Ilexshadow/Cyber-Wand/外壳/3DShell_实物图.jpg

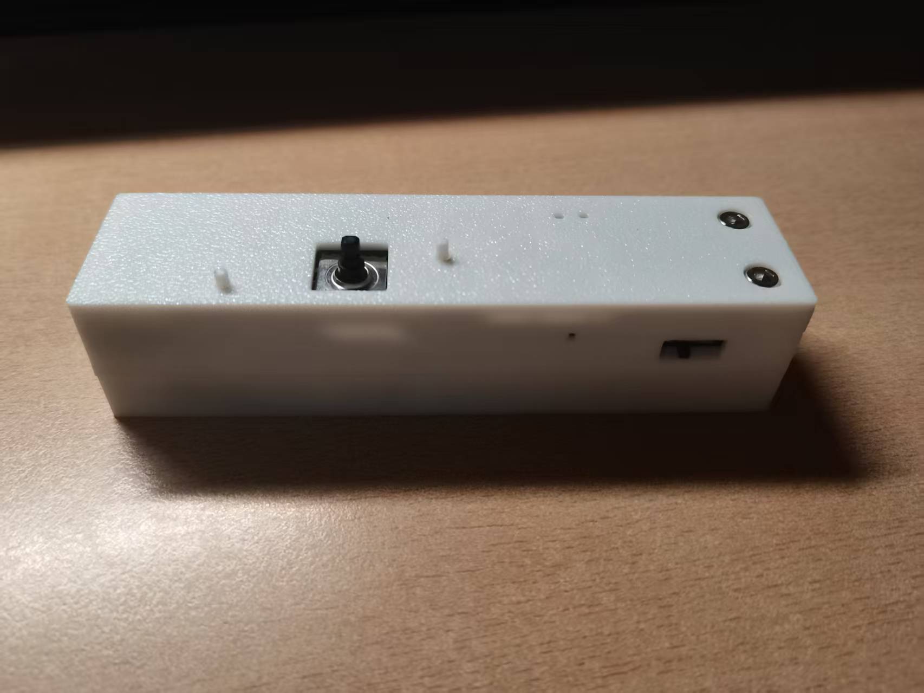
外壳/3DShell_实物图.jpg
