Ilexshadow/Cyber-Wand/代码/C程序-发送-PCB/nnom/weights.h

#include "nnom.h"

/* Weights, bias and Q format */
#define TENSOR_CONV1D_KERNEL_0 {24, 74, 75, -38, 81, 41, -17, 33, -9, 38, -53, -88, -45, -43, -19, 26, -67, -12, -23, 24, 47, -24, 77, 69, -91, 19, 64, -34, -36, -29, -68, -21, 91, -102, -52, 71, -4, -78, -80, 20, -27, 8, 53, -16, -89, 46, -78, -74, 29, -91, -8, 66, -28, -76, 71, 88, -6, 79, 59, -72, 84, 17, -30, -14, 63, 70, 10, 20, 75, 26, 49, 95, 33, 76, -37, 68, 94, 9, -46, 72, -27, -81, 10, -36, -57, 58, -7, 25, -54, -65, -55, 90, 58, -35, 82, 52, -97, 55, 67, -45, 40, 36, 65, -48, 109, 7, -67, 71, 38, 94, 43, 60, 52, 95, 53, 4, 32, 4, -19, 24, -31, -104, -86, 80, -82, -50, 56, -8, 74, -4, 45, 63, 80, -55, 1, -92, 30, 80, -54, -71, 81, -10, 9, 98, 7, -47, -97, -27, -9, -29, -87, 54, -83, -72, 21, 86, -43, 37, 102, 31, -45, 54, -25, -49, 85, -55, -89, 89, -100, -30, 37, -17, 14, -57, 55, -70, -68, -27, -44, -10, -30, -23, 25, -93, -59, -19, -59, -58, 45, 90, -30, 48, 32, 11, -7, 24, -73, -4, -96, -79, 21, -84, -76, -10, -105, 26, -7, -28, -100, -86, 37, -12, -50, 74, -80, -71, -102, -28, 77, -88, -70, 1, -66, -45, 35, -71, -40, -5, -90, -55, -20, -29, -18, 8, 37, 100, 99, -8, 51, 29, -4, 72, -12, 88, 83, -37, 57, -8, 66, 1, 36, 38, 28, -71, 42, -6, 35, 91, -49, -50, 50, 36, 73, -70, 85, 68, 33, 35, 34, -60}

#define TENSOR_CONV1D_KERNEL_0_DEC_BITS {8}

#define TENSOR_CONV1D_BIAS_0 {53, -39, 70, 80, -25, 23, 57, 27, 62, 25, 84, 23, 90, -16, 74, 57, 85, 75, 75, -38, 33, 36, 43, 10, 25, 35, 87, 102, 13, 92}

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

#define TENSOR_CONV1D_1_KERNEL_0_DEC_BITS {8}

#define TENSOR_CONV1D_1_BIAS_0 {98, 0, 14, 12, 70, 1, 92, -38, -54, 19, 69, 53, -55, 108, -18}

#define TENSOR_CONV1D_1_BIAS_0_DEC_BITS {10}

#define CONV1D_1_BIAS_LSHIFT {2}

#define CONV1D_1_OUTPUT_RSHIFT {9}

#define TENSOR_DENSE_KERNEL_0 {34, 87, -73, 34, 6, -62, 37, -13, -118, 4, 98, 1, 45, 20, 36, -55, -52, -46, 45, 43, -49, 27, 8, -63, 10, -16, 31, 30, -91, 23, -55, -7, 11, 7, -45, 41, -36, 42, -44, 14, -32, 23, -126, -17, 67, -1, -14, -33, -31, -14, -61, -57, -4, 53, 30, -97, -75, 19, 48, 28, -23, 44, 83, 9, -6, 92, 7, -50, 3, -35, 40, -26, 95, 90, -21, 56, 4, 32, -27, -24, 65, -112, 59, -65, 88, -54, 77, -80, -18, -22, 24, -82, -108, 50, 73, 18, -112, 78, 82, 16, 37, 36, -36, 30, -24, 93, 42, 52, -67, -9, 90, 36, 55, 87, -19, 64, -71, -31, 22, -65, 30, -32, 64, -86, -35, 7, -109, 104, -14, 27, -22, -34, 33, 109, -114, 24, -114, -54, -11, -109, 34, -17, -62, -103, 55, 14, 3, 22, -22, -81, 65, 3, -78, -41, 74, -38, -21, 83, 47, 52, 80, 9, -17, 17, 0, -86, -96, 66, -94, -33, -27, -40, 82, -14, -5, 84, 100, -87, 82, 51, 45, 8, -32, 41, 17, -3, 10, 79, -51, -54, -68, -14, -75, -56, -43, -34, -114, 19, 14, -99, 32, 52, 63, -91, 38, -111, 16, -21, -4, 13, -28, -32, -58, 0, -79, 60, -44, -90, 2, -18, -65, 84, -89, 11, -60, -112, 91, 45, -102, 1, -100, -33, 28, -90, 57, -109, 43, -61, 33, -49, -44, 54, 48, -10, 19, 7, 74, -17, -49, 2, 8, 1, 91, 24, 79, -53, 80, -58, -77, 0, 8, -17, 90, -76, -35, -58, 54, -49, -122, -52, -3, 63, -17, 60, -78, -28, -4, -56, -29, -91, -113, 73, -52, 27, -46, -20, 15, -10, 95, -106, 75, -88, -102, 25, -111, 35, -28, 52, -76, 38, 17, 5, 73, 6, -30, -8, 21, 26, 19, -57, -73, 67, 16, -35, 16, 33, -88, -23, 49, -67, -56, 7, 94, 91, 61, 6, -103, -1, -37, 11, -1, -40, -88, 47, -57, 10, 5, -68, 50, -48, 69, 58, -101, 22, 61, 44, 43, -3, 28, 20, -62, 18, -28, -75, -11, -41, -71, -95, 15, 49, -47, 72, -73, -24, 84, -19, 47, -16, -7, -54, 38, -89, 52, -66, -3, 66, 53, -20, -7, -25, -88, -66, 33, 59, -53, -17, -69, 45, 85, 73, 47, -52, 34, -46, 20, 21, -66, 20, -94, -77, -16, -21, -42, 16, 9, 49, 8, -28, -3, -6, 106, 32, 16, 92, 51, 9, 36, -60, 80, 66, 28, 85, -23, -71, -5, 13, 72, -45, 86, -32, 50, -3, -34, 73, 10, -11, 22, -78, 9, -4, -8, -73, 79, 26, -32, -64, 87, 53, 4, 85, -71, 72, 12, 51, 30, 24, -3, 29, 47, 1, -35, 67, 63, 59, 87, 43, 117, -59, -7, 52, 70, -87, -100, 77, -70, -124, -27, 16, 8, -7, 84, -46, 57, -90, 41, 75, -72, -39, -67, -46, -45, -84, 20, -68, 96, -12, -39, -37, 52, 30, -47, 40, -41, 67, -28, 61, 78, 37, 64, -93, 87, -80, -3, 37, -98, -64, -60, 37, -23, -74, -2, 4, -42, -42, -85, -87, -28, -75, -35, 8, 74, -118, -24, -5, 104, -9, -73, 50, -34, -88, -38, 8, 16, 11, 1, 43, 9, -6, 38, 6, 34, 61, -6, 23, -11, -109, -57, 26, 34, -37, -13, -46, -98, -73, -72, 81, 23, -6, -67, 55, -65, -38, 52, 61, -20, -10, 64, 49, 71, -103, 42, 82, 59, -36, -23, -44, 16, 84, -41, 60, 45, -62, -22, 82, -116, 100, -37, 37, -24, 17}

#define TENSOR_DENSE_KERNEL_0_DEC_BITS {8}

#define TENSOR_DENSE_BIAS_0 {-44, 81, -31, -89, -63, -3, 64, 24, 40, 24}

#define TENSOR_DENSE_BIAS_0_DEC_BITS {10}

#define DENSE_BIAS_LSHIFT {1}

#define DENSE_OUTPUT_RSHIFT {9}


/* output q format for each layer */
#define INPUT_1_OUTPUT_DEC 5
#define INPUT_1_OUTPUT_OFFSET 0
#define CONV1D_OUTPUT_DEC 4
#define CONV1D_OUTPUT_OFFSET 0
#define LEAKY_RE_LU_OUTPUT_DEC 4
#define LEAKY_RE_LU_OUTPUT_OFFSET 0
#define CONV1D_1_OUTPUT_DEC 3
#define CONV1D_1_OUTPUT_OFFSET 0
#define LEAKY_RE_LU_1_OUTPUT_DEC 3
#define LEAKY_RE_LU_1_OUTPUT_OFFSET 0
#define MAX_POOLING1D_OUTPUT_DEC 3
#define MAX_POOLING1D_OUTPUT_OFFSET 0
#define FLATTEN_OUTPUT_DEC 3
#define FLATTEN_OUTPUT_OFFSET 0
#define DENSE_OUTPUT_DEC 2
#define DENSE_OUTPUT_OFFSET 0
#define SOFTMAX_OUTPUT_DEC 7
#define SOFTMAX_OUTPUT_OFFSET 0

/* bias shift and output shift for none-weighted layer */

/* tensors and configurations for each layer */
static int8_t nnom_input_data[300] = {0};

const nnom_shape_data_t tensor_input_1_dim[] = {100, 3};
const nnom_qformat_param_t tensor_input_1_dec[] = {5};
const nnom_qformat_param_t tensor_input_1_offset[] = {0};
const nnom_tensor_t tensor_input_1 = {
    .p_data = (void*)nnom_input_data,
    .dim = (nnom_shape_data_t*)tensor_input_1_dim,
    .q_dec = (nnom_qformat_param_t*)tensor_input_1_dec,
    .q_offset = (nnom_qformat_param_t*)tensor_input_1_offset,
    .qtype = NNOM_QTYPE_PER_TENSOR,
    .num_dim = 2,
    .bitwidth = 8
};

const nnom_io_config_t input_1_config = {
    .super = {.name = "input_1"},
    .tensor = (nnom_tensor_t*)&tensor_input_1
};
const int8_t tensor_conv1d_kernel_0_data[] = TENSOR_CONV1D_KERNEL_0;

const nnom_shape_data_t tensor_conv1d_kernel_0_dim[] = {3, 3, 30};
const nnom_qformat_param_t tensor_conv1d_kernel_0_dec[] = TENSOR_CONV1D_KERNEL_0_DEC_BITS;
const nnom_qformat_param_t tensor_conv1d_kernel_0_offset[] = {0};
const nnom_tensor_t tensor_conv1d_kernel_0 = {
    .p_data = (void*)tensor_conv1d_kernel_0_data,
    .dim = (nnom_shape_data_t*)tensor_conv1d_kernel_0_dim,
    .q_dec = (nnom_qformat_param_t*)tensor_conv1d_kernel_0_dec,
    .q_offset = (nnom_qformat_param_t*)tensor_conv1d_kernel_0_offset,
    .qtype = NNOM_QTYPE_PER_TENSOR,
    .num_dim = 3,
    .bitwidth = 8
};
const int8_t tensor_conv1d_bias_0_data[] = TENSOR_CONV1D_BIAS_0;

const nnom_shape_data_t tensor_conv1d_bias_0_dim[] = {30};
const nnom_qformat_param_t tensor_conv1d_bias_0_dec[] = TENSOR_CONV1D_BIAS_0_DEC_BITS;
const nnom_qformat_param_t tensor_conv1d_bias_0_offset[] = {0};
const nnom_tensor_t tensor_conv1d_bias_0 = {
    .p_data = (void*)tensor_conv1d_bias_0_data,
    .dim = (nnom_shape_data_t*)tensor_conv1d_bias_0_dim,
    .q_dec = (nnom_qformat_param_t*)tensor_conv1d_bias_0_dec,
    .q_offset = (nnom_qformat_param_t*)tensor_conv1d_bias_0_offset,
    .qtype = NNOM_QTYPE_PER_TENSOR,
    .num_dim = 1,
    .bitwidth = 8
};

const nnom_qformat_param_t conv1d_output_shift[] = CONV1D_OUTPUT_RSHIFT;
const nnom_qformat_param_t conv1d_bias_shift[] = CONV1D_BIAS_LSHIFT;
const nnom_conv2d_config_t conv1d_config = {
    .super = {.name = "conv1d"},
    .qtype = NNOM_QTYPE_PER_TENSOR,
    .weight = (nnom_tensor_t*)&tensor_conv1d_kernel_0,
    .bias = (nnom_tensor_t*)&tensor_conv1d_bias_0,
    .output_shift = (nnom_qformat_param_t *)&conv1d_output_shift, 
    .bias_shift = (nnom_qformat_param_t *)&conv1d_bias_shift, 
    .filter_size = 30,
    .kernel_size = {3},
    .stride_size = {3},
    .padding_size = {0, 0},
    .dilation_size = {1},
    .padding_type = PADDING_SAME
};
const int8_t tensor_conv1d_1_kernel_0_data[] = TENSOR_CONV1D_1_KERNEL_0;

const nnom_shape_data_t tensor_conv1d_1_kernel_0_dim[] = {3, 30, 15};
const nnom_qformat_param_t tensor_conv1d_1_kernel_0_dec[] = TENSOR_CONV1D_1_KERNEL_0_DEC_BITS;
const nnom_qformat_param_t tensor_conv1d_1_kernel_0_offset[] = {0};
const nnom_tensor_t tensor_conv1d_1_kernel_0 = {
    .p_data = (void*)tensor_conv1d_1_kernel_0_data,
    .dim = (nnom_shape_data_t*)tensor_conv1d_1_kernel_0_dim,
    .q_dec = (nnom_qformat_param_t*)tensor_conv1d_1_kernel_0_dec,
    .q_offset = (nnom_qformat_param_t*)tensor_conv1d_1_kernel_0_offset,
    .qtype = NNOM_QTYPE_PER_TENSOR,
    .num_dim = 3,
    .bitwidth = 8
};
const int8_t tensor_conv1d_1_bias_0_data[] = TENSOR_CONV1D_1_BIAS_0;

const nnom_shape_data_t tensor_conv1d_1_bias_0_dim[] = {15};
const nnom_qformat_param_t tensor_conv1d_1_bias_0_dec[] = TENSOR_CONV1D_1_BIAS_0_DEC_BITS;
const nnom_qformat_param_t tensor_conv1d_1_bias_0_offset[] = {0};
const nnom_tensor_t tensor_conv1d_1_bias_0 = {
    .p_data = (void*)tensor_conv1d_1_bias_0_data,
    .dim = (nnom_shape_data_t*)tensor_conv1d_1_bias_0_dim,
    .q_dec = (nnom_qformat_param_t*)tensor_conv1d_1_bias_0_dec,
    .q_offset = (nnom_qformat_param_t*)tensor_conv1d_1_bias_0_offset,
    .qtype = NNOM_QTYPE_PER_TENSOR,
    .num_dim = 1,
    .bitwidth = 8
};

const nnom_qformat_param_t conv1d_1_output_shift[] = CONV1D_1_OUTPUT_RSHIFT;
const nnom_qformat_param_t conv1d_1_bias_shift[] = CONV1D_1_BIAS_LSHIFT;
const nnom_conv2d_config_t conv1d_1_config = {
    .super = {.name = "conv1d_1"},
    .qtype = NNOM_QTYPE_PER_TENSOR,
    .weight = (nnom_tensor_t*)&tensor_conv1d_1_kernel_0,
    .bias = (nnom_tensor_t*)&tensor_conv1d_1_bias_0,
    .output_shift = (nnom_qformat_param_t *)&conv1d_1_output_shift, 
    .bias_shift = (nnom_qformat_param_t *)&conv1d_1_bias_shift, 
    .filter_size = 15,
    .kernel_size = {3},
    .stride_size = {3},
    .padding_size = {0, 0},
    .dilation_size = {1},
    .padding_type = PADDING_SAME
};

const nnom_pool_config_t max_pooling1d_config = {
    .super = {.name = "max_pooling1d"},
    .padding_type = PADDING_VALID,
    .output_shift = 0,
    .kernel_size = {3},
    .stride_size = {3},
    .num_dim = 1
};

const nnom_flatten_config_t flatten_config = {
    .super = {.name = "flatten"}
};
const int8_t tensor_dense_kernel_0_data[] = TENSOR_DENSE_KERNEL_0;

const nnom_shape_data_t tensor_dense_kernel_0_dim[] = {60, 10};
const nnom_qformat_param_t tensor_dense_kernel_0_dec[] = TENSOR_DENSE_KERNEL_0_DEC_BITS;
const nnom_qformat_param_t tensor_dense_kernel_0_offset[] = {0};
const nnom_tensor_t tensor_dense_kernel_0 = {
    .p_data = (void*)tensor_dense_kernel_0_data,
    .dim = (nnom_shape_data_t*)tensor_dense_kernel_0_dim,
    .q_dec = (nnom_qformat_param_t*)tensor_dense_kernel_0_dec,
    .q_offset = (nnom_qformat_param_t*)tensor_dense_kernel_0_offset,
    .qtype = NNOM_QTYPE_PER_TENSOR,
    .num_dim = 2,
    .bitwidth = 8
};
const int8_t tensor_dense_bias_0_data[] = TENSOR_DENSE_BIAS_0;

const nnom_shape_data_t tensor_dense_bias_0_dim[] = {10};
const nnom_qformat_param_t tensor_dense_bias_0_dec[] = TENSOR_DENSE_BIAS_0_DEC_BITS;
const nnom_qformat_param_t tensor_dense_bias_0_offset[] = {0};
const nnom_tensor_t tensor_dense_bias_0 = {
    .p_data = (void*)tensor_dense_bias_0_data,
    .dim = (nnom_shape_data_t*)tensor_dense_bias_0_dim,
    .q_dec = (nnom_qformat_param_t*)tensor_dense_bias_0_dec,
    .q_offset = (nnom_qformat_param_t*)tensor_dense_bias_0_offset,
    .qtype = NNOM_QTYPE_PER_TENSOR,
    .num_dim = 1,
    .bitwidth = 8
};

const nnom_qformat_param_t dense_output_shift[] = DENSE_OUTPUT_RSHIFT;
const nnom_qformat_param_t dense_bias_shift[] = DENSE_BIAS_LSHIFT;
const nnom_dense_config_t dense_config = {
    .super = {.name = "dense"},
    .qtype = NNOM_QTYPE_PER_TENSOR,
    .weight = (nnom_tensor_t*)&tensor_dense_kernel_0,
    .bias = (nnom_tensor_t*)&tensor_dense_bias_0,
    .output_shift = (nnom_qformat_param_t *)&dense_output_shift,
    .bias_shift = (nnom_qformat_param_t *)&dense_bias_shift
};

const nnom_softmax_config_t softmax_config = {
    .super = {.name = "softmax"}
};
static int8_t nnom_output_data[10] = {0};

const nnom_shape_data_t tensor_output0_dim[] = {10};
const nnom_qformat_param_t tensor_output0_dec[] = {SOFTMAX_OUTPUT_DEC};
const nnom_qformat_param_t tensor_output0_offset[] = {0};
const nnom_tensor_t tensor_output0 = {
    .p_data = (void*)nnom_output_data,
    .dim = (nnom_shape_data_t*)tensor_output0_dim,
    .q_dec = (nnom_qformat_param_t*)tensor_output0_dec,
    .q_offset = (nnom_qformat_param_t*)tensor_output0_offset,
    .qtype = NNOM_QTYPE_PER_TENSOR,
    .num_dim = 1,
    .bitwidth = 8
};

const nnom_io_config_t output0_config = {
    .super = {.name = "output0"},
    .tensor = (nnom_tensor_t*)&tensor_output0
};
/* model version */
#define NNOM_MODEL_VERSION (10000*0 + 100*4 + 3)

/* nnom model */
static nnom_model_t* nnom_model_create(void)
{
	static nnom_model_t model;
	nnom_layer_t* layer[10];

	check_model_version(NNOM_MODEL_VERSION);
	new_model(&model);

	layer[0] = input_s(&input_1_config);
	layer[1] = model.hook(conv2d_s(&conv1d_config), layer[0]);
	layer[2] = model.active(act_leaky_relu(0.300000f), layer[1]);
	layer[3] = model.hook(conv2d_s(&conv1d_1_config), layer[2]);
	layer[4] = model.active(act_leaky_relu(0.300000f), layer[3]);
	layer[5] = model.hook(maxpool_s(&max_pooling1d_config), layer[4]);
	layer[6] = model.hook(flatten_s(&flatten_config), layer[5]);
	layer[7] = model.hook(dense_s(&dense_config), layer[6]);
	layer[8] = model.hook(softmax_s(&softmax_config), layer[7]);
	layer[9] = model.hook(output_s(&output0_config), layer[8]);
	model_compile(&model, layer[0], layer[9]);
	return &model;
}
