Ilexshadow/Cyber-Wand/代码/C程序-发送-PCB/Hardware/MyI2C.h

#ifndef _MYI2C_H
#define _MYI2C_H

void MyI2C_W_SCL(uint8_t BitValue);
void MyI2C_W_SDA(uint8_t BitValue);
uint8_t MyI2C_R_SDA(void);

void MyI2C_Init(void);//I2C初始化

void MyI2C_Start(void);
void MyI2C_Stop(void);

void MyI2C_SendByte(uint8_t Byte);
uint8_t MyI2C_ReceiveByte(void);

void MyI2C_SendAck(uint8_t AckBit);
uint8_t MyI2C_ReceiveAck(void);
	
#endif
