Ilexshadow/Cyber-Wand/代码/C程序-录制数据-PCB/Handware/LED.c

#include "stm32f10x.h"                  // Device header

void LED_Init(void)
{
	RCC_APB2PeriphClockCmd(RCC_APB2Periph_GPIOA,ENABLE);
	
	GPIO_InitTypeDef GPIO_InitStruct;
	GPIO_InitStruct.GPIO_Mode = GPIO_Mode_Out_PP;
	GPIO_InitStruct.GPIO_Pin =GPIO_Pin_1|GPIO_Pin_2;
	GPIO_InitStruct.GPIO_Speed =GPIO_Speed_50MHz;
	GPIO_Init(GPIOA,&GPIO_InitStruct);
}

void LED1_ON(void)
{
	GPIO_ResetBits(GPIOA,GPIO_Pin_1);
}
void LED1_OFF(void)
{
	GPIO_SetBits(GPIOA,GPIO_Pin_1);
}
void LED1_Turn(void)
{
	if(GPIO_ReadOutputDataBit(GPIOA,GPIO_Pin_1) == 0)
	{
		GPIO_SetBits(GPIOA,GPIO_Pin_1);
	}
	else  
	{
		GPIO_ResetBits(GPIOA,GPIO_Pin_1);
	}
		//注意：else不能写成
	  //if(GPIO_ReadOutputDataBit(GPIOA,GPIO_Pin_1) == 1)
		//因为高电平是非0但不一定是1，而低电平一定是0
		//下面的LED2_Turn()同理
}

void LED2_ON(void)
{
	GPIO_ResetBits(GPIOA,GPIO_Pin_2);
}
void LED2_OFF(void)
{
	GPIO_SetBits(GPIOA,GPIO_Pin_2);
}
void LED2_Turn(void)
{
	if(GPIO_ReadOutputDataBit(GPIOA,GPIO_Pin_2) == 0)
	{
		GPIO_SetBits(GPIOA,GPIO_Pin_2);
	}
	else
	{
		GPIO_ResetBits(GPIOA,GPIO_Pin_2);
	}
}
