Ilexshadow/Cyber-Wand/代码/Python程序-数据训练-PCB/split_data.py

from sklearn.model_selection import train_test_split


def split_data(X,y):
    
    X_train, X_test, y_train, y_test = train_test_split(
        X, y, 
        test_size=0.2, 
        random_state=42, 
        stratify=y
    )

    return X_train, X_test, y_train, y_test
